canberkdurmus/microlab-2/image/1.jpg

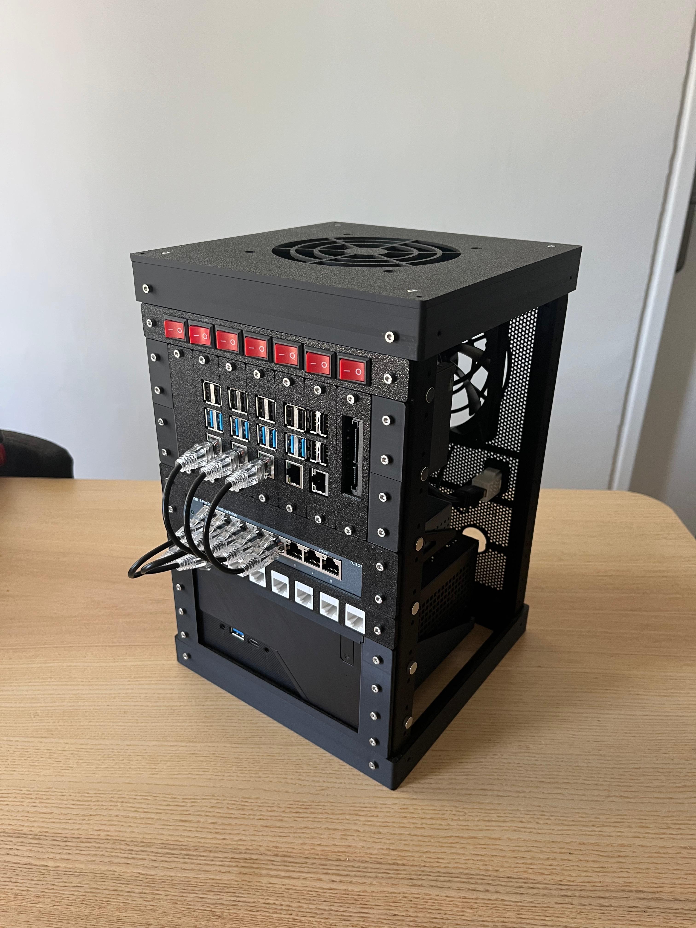
image/1.jpg
