canberkdurmus/microlab-2/image/2.jpg

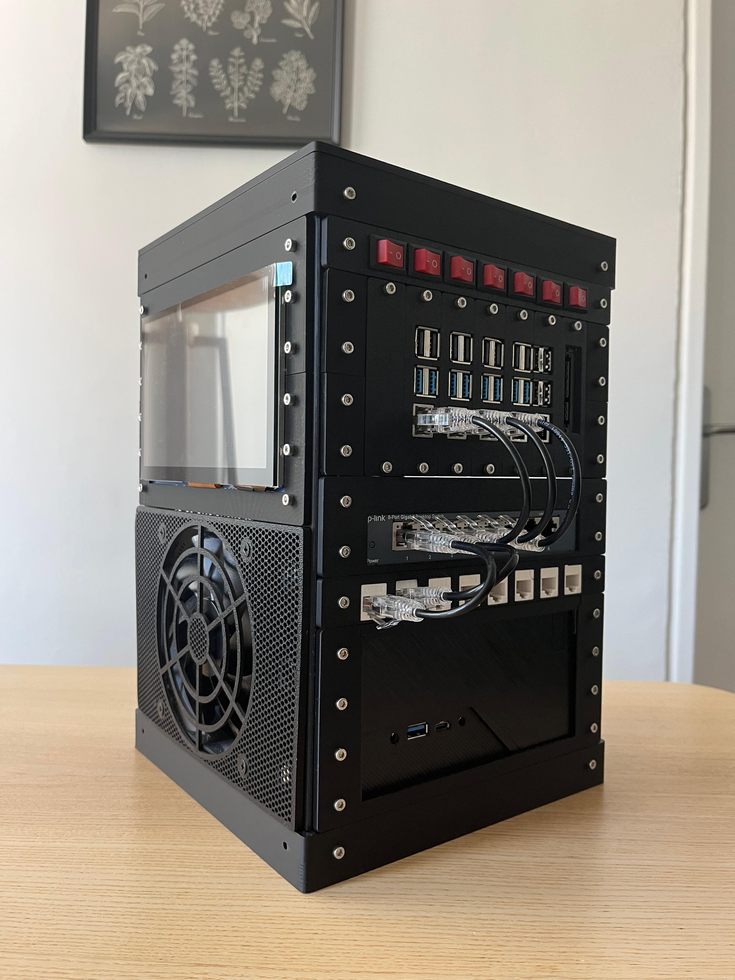
image/2.jpg
