canberkdurmus/microlab-2/image/4.jpg

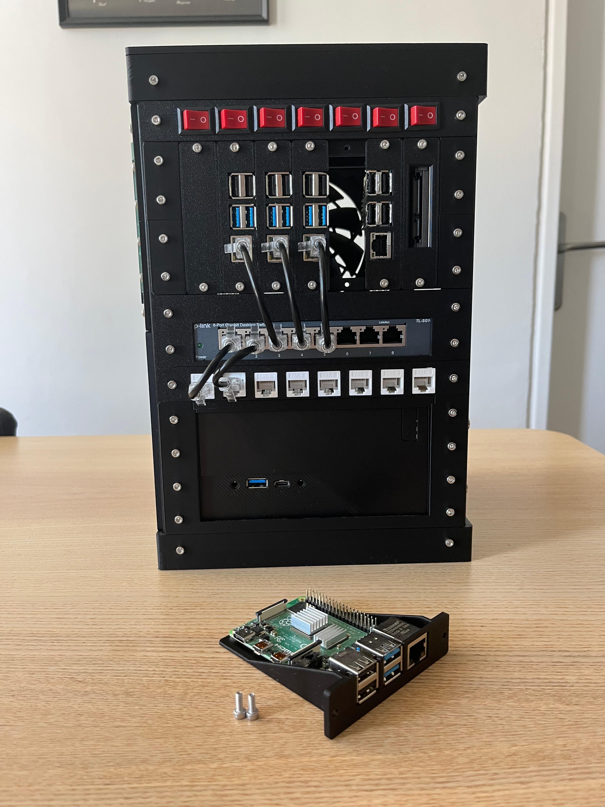
image/4.jpg
