canberkdurmus/microlab-2/image/5.jpg

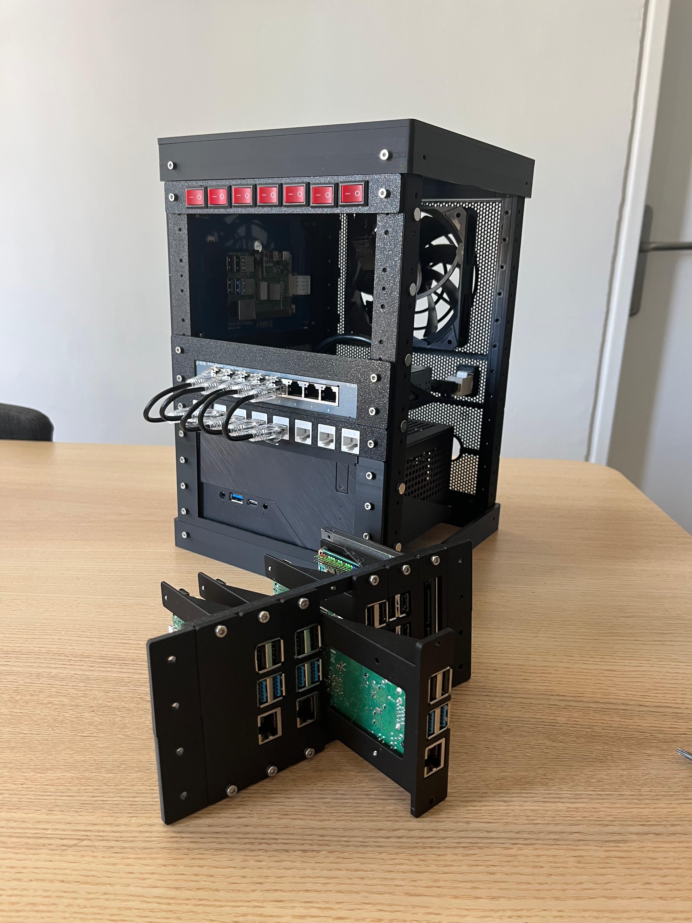
image/5.jpg
