canberkdurmus/microlab-2/image/6.jpg

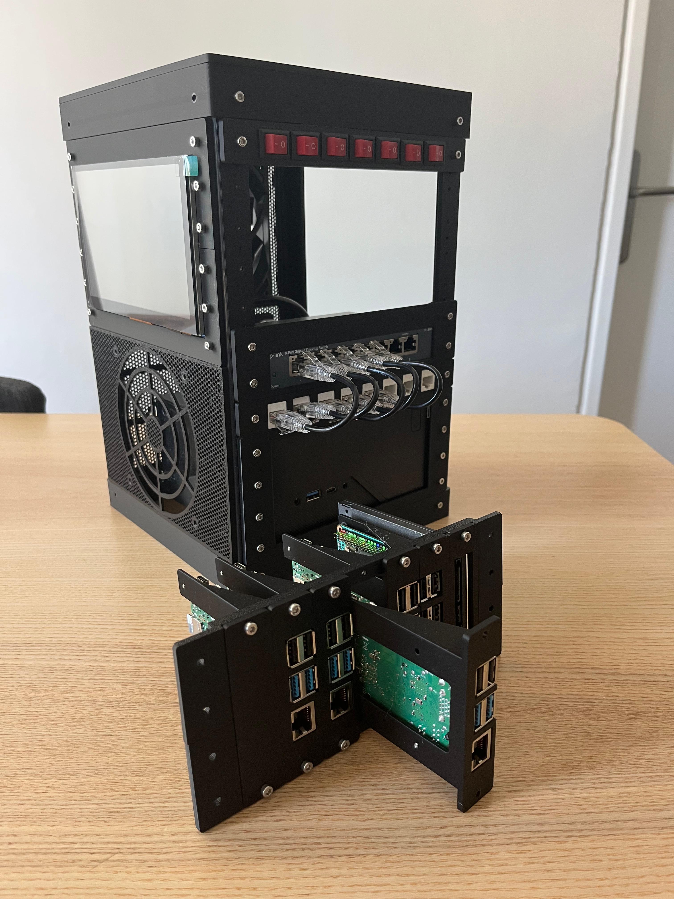
image/6.jpg
