canberkdurmus/microlab-2/image/7.jpg

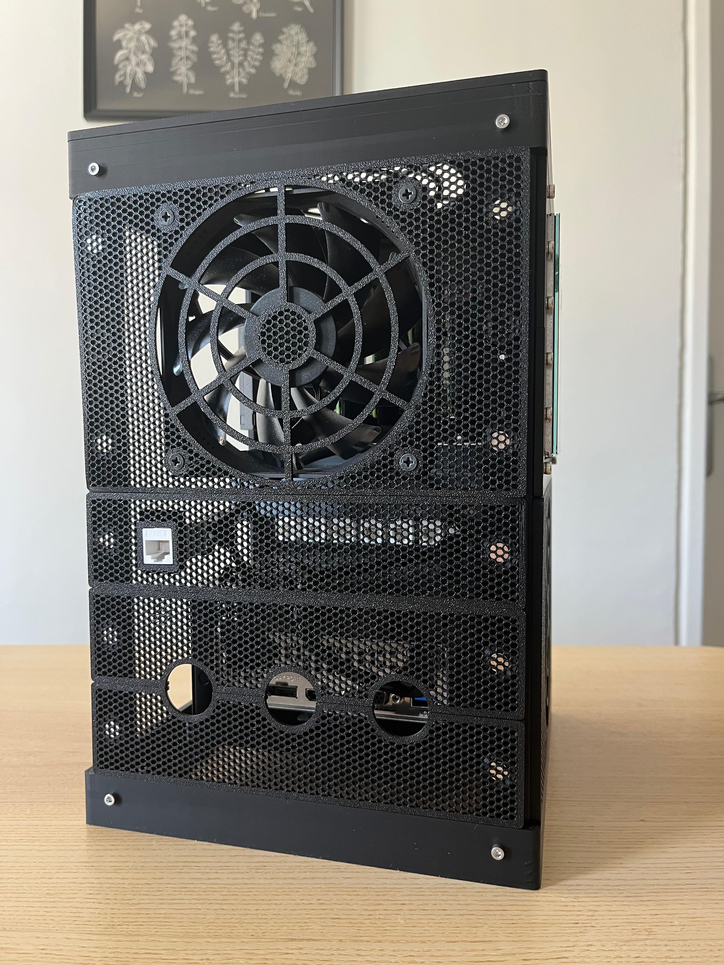
image/7.jpg
