canberkdurmus/microlab-2/image/8.jpg

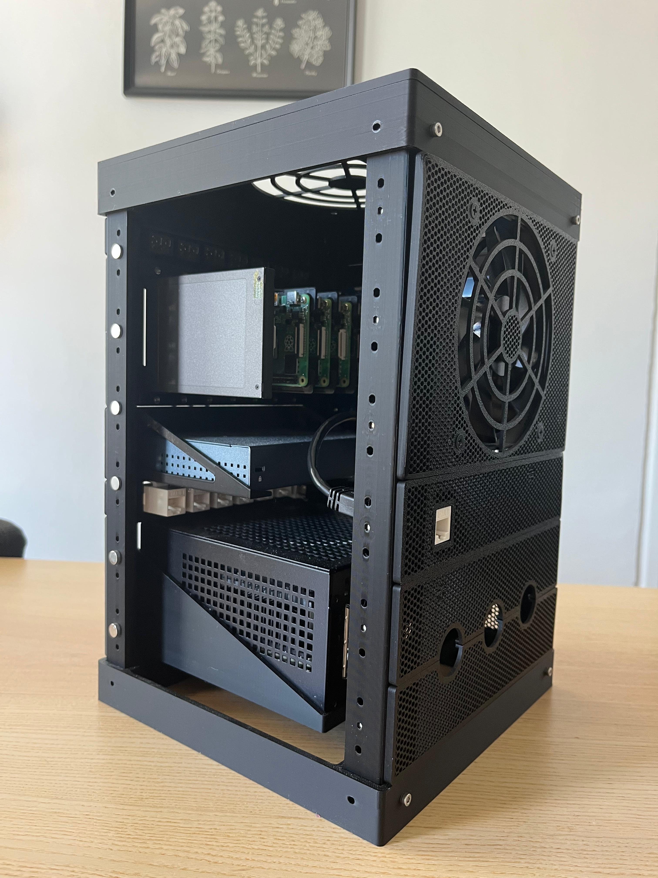
image/8.jpg
