canberkdurmus/microlab-2/image/9.jpg

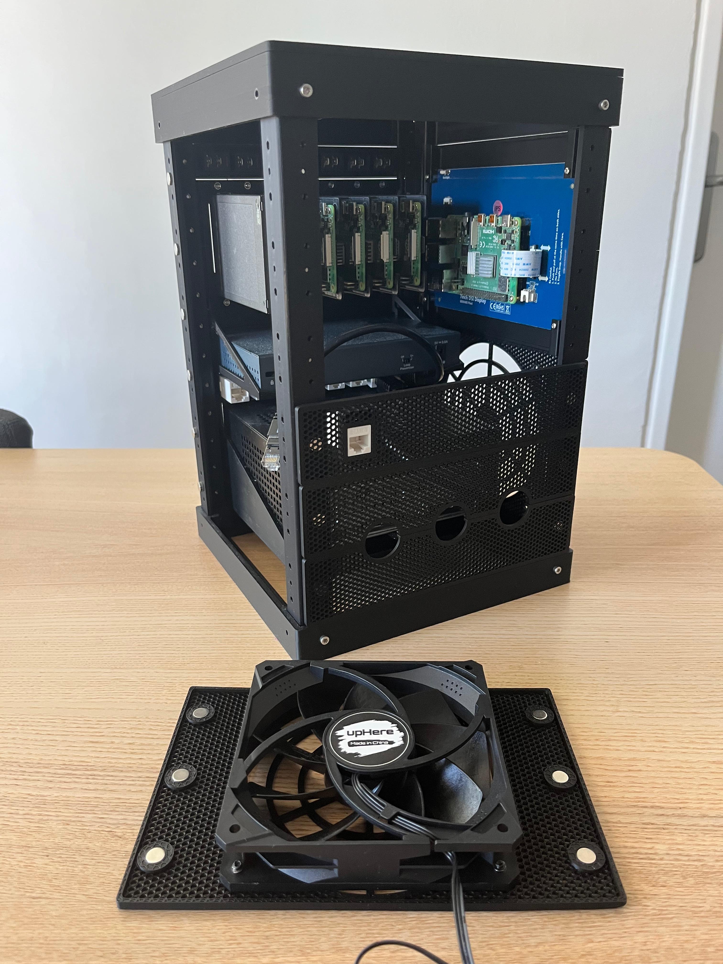
image/9.jpg
