canberkdurmus/microlab-2/image/10.jpg

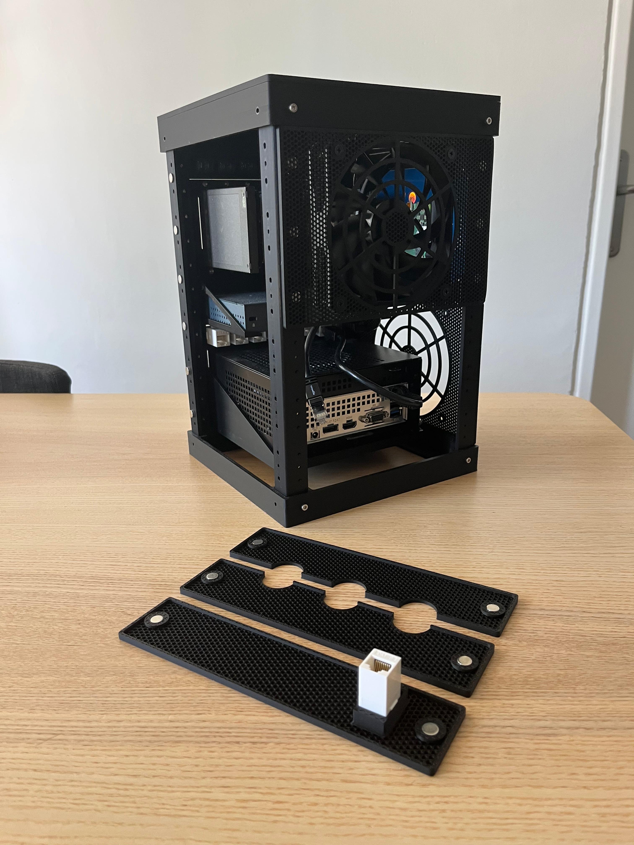
image/10.jpg
