canberkdurmus/microlab-2/image/11.jpg

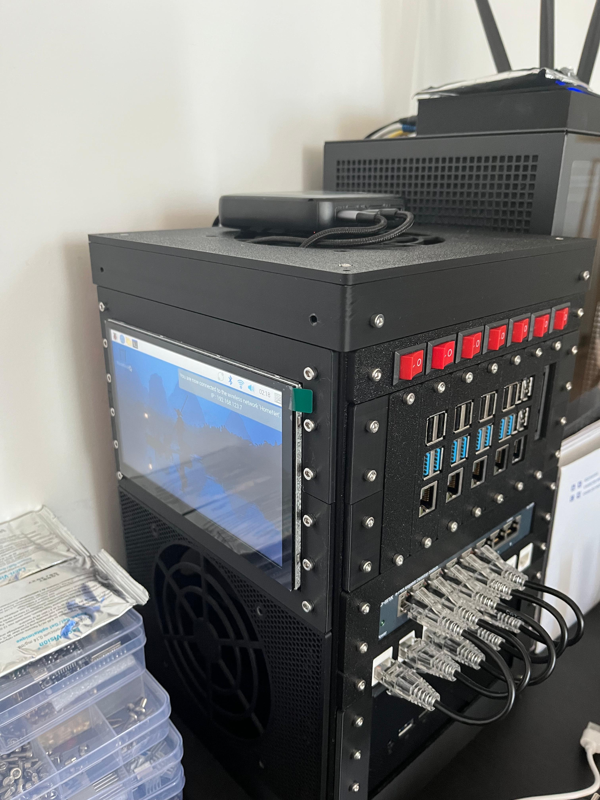
image/11.jpg
