canberkdurmus/microlab-2/step/Tray-0.5U-Template-Starter.step

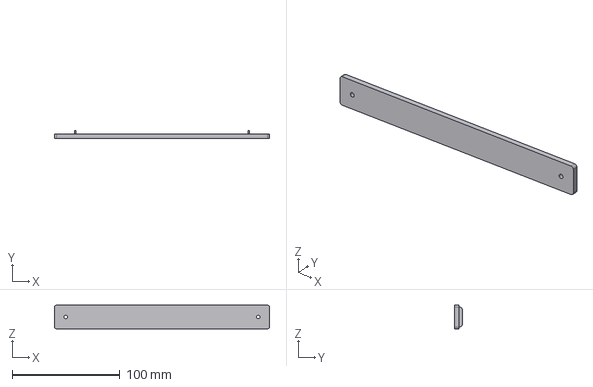
[picture p27: CAD file, 2025-09-13]
step/Tray-0.5U-Template-Starter.step
199.8 x 7.00 x 22.2 mm
