canberkdurmus/microlab-2/step/Extension-ITX-5U.step

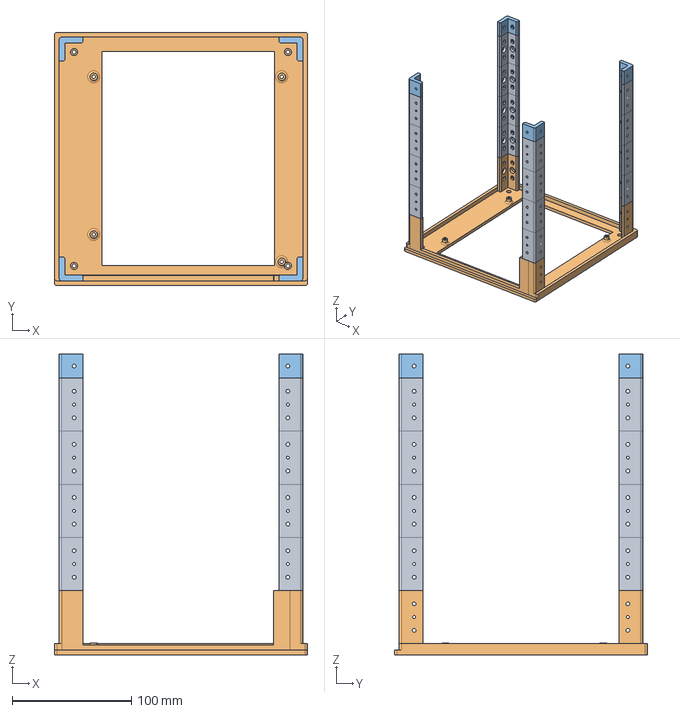
[picture p28: CAD file, 2025-09-13]
step/Extension-ITX-5U.step
212.0 x 212.0 x 252.1 mm
