canberkdurmus/microlab-2/step/Panel-1U-Button12mm.step

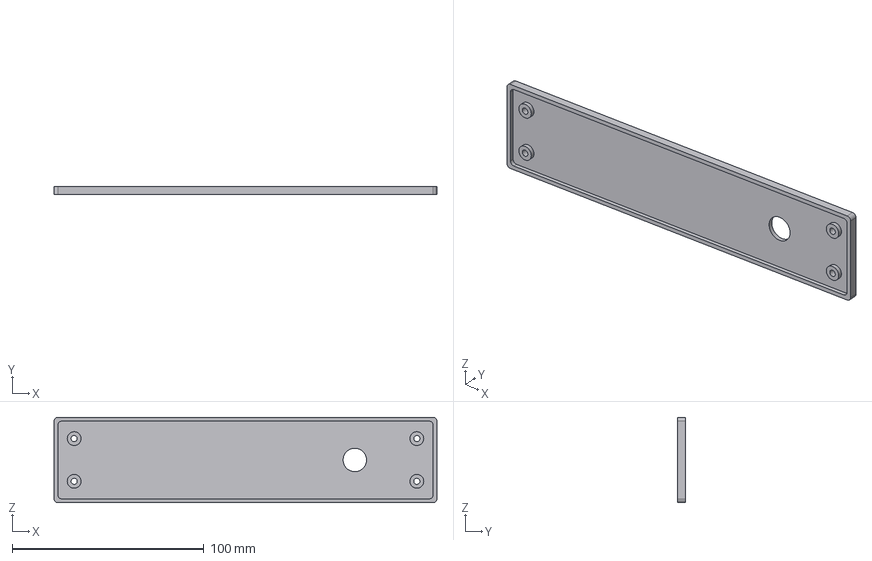
[picture p29: CAD file, 2025-09-13]
step/Panel-1U-Button12mm.step
199.6 x 4.00 x 44.4 mm
