canberkdurmus/microlab-2/step/Panel-3U-Disp7-Top.step

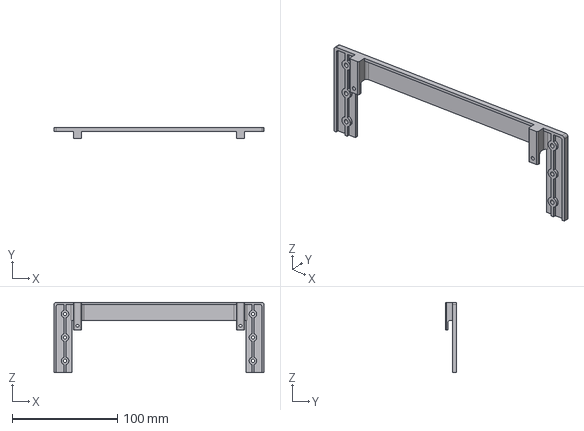
[picture p30: CAD file, 2025-09-13]
step/Panel-3U-Disp7-Top.step
199.6 x 10.5 x 66.7 mm
