canberkdurmus/microlab-2/step/Panel-1U-Mag-fan-40x3.step

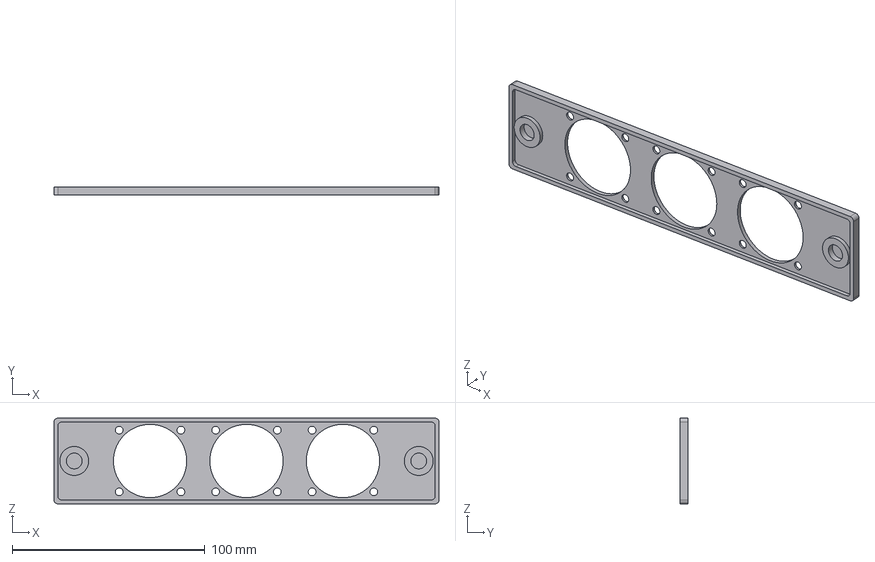
[picture p31: CAD file, 2025-09-13]
step/Panel-1U-Mag-fan-40x3.step
199.6 x 4.00 x 44.4 mm
