canberkdurmus/microlab-2/step/Tray-1U-Switch-TpLink-TLSG108.step

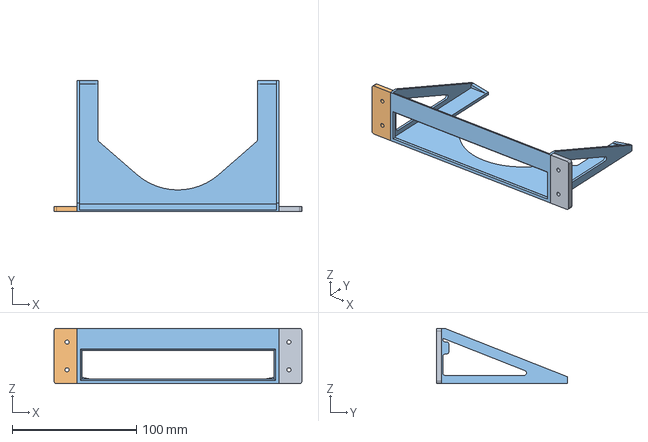
[picture p32: CAD file, 2025-09-13]
step/Tray-1U-Switch-TpLink-TLSG108.step
199.6 x 105.8 x 44.4 mm
