canberkdurmus/microlab-2/step/Tray-2U-X300.step

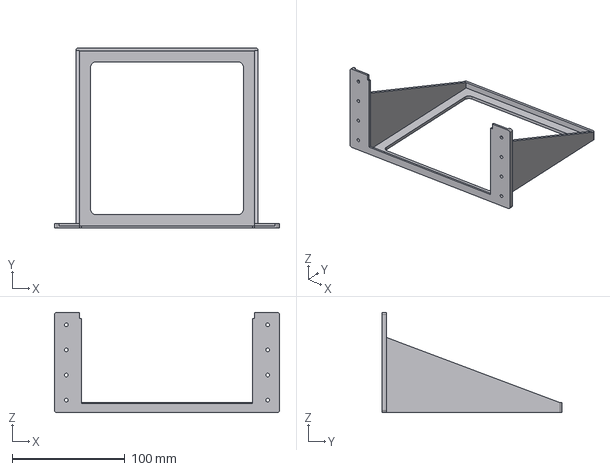
[picture p33: CAD file, 2025-09-13]
step/Tray-2U-X300.step
199.6 x 160.0 x 88.9 mm
