canberkdurmus/microlab-2/step/Mini-Tray-0.5-Blank.step

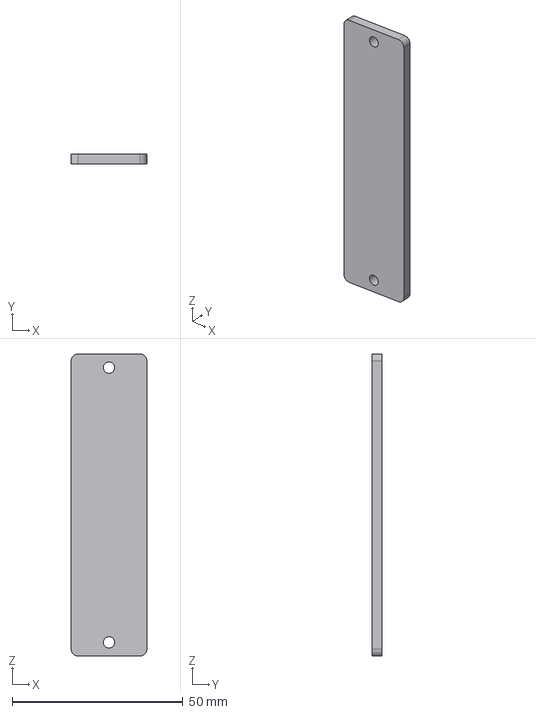
[picture p34: CAD file, 2025-09-13]
step/Mini-Tray-0.5-Blank.step
22.2 x 3.00 x 88.5 mm
