canberkdurmus/microlab-2/step/Extension-ITX-1U.step

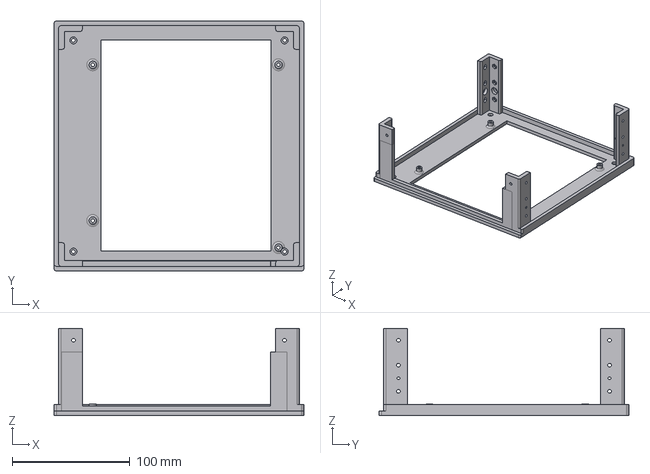
[picture p35: CAD file, 2025-09-13]
step/Extension-ITX-1U.step
212.0 x 212.0 x 74.1 mm
