canberkdurmus/microlab-2/step/Panel-3U-Solid.step

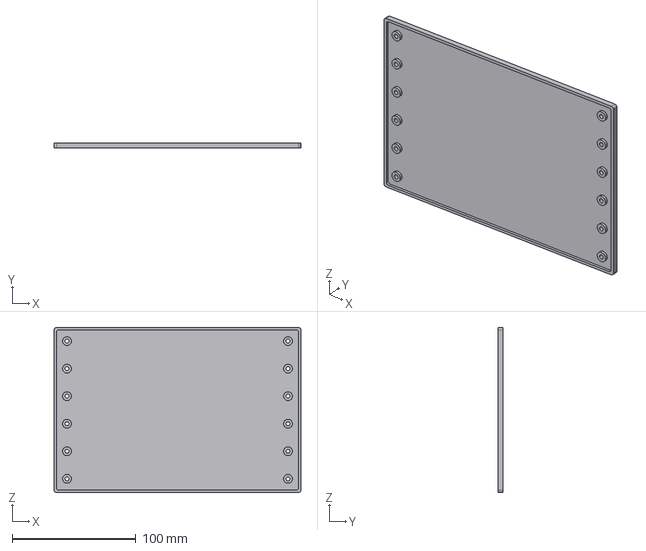
[picture p36: CAD file, 2025-09-13]
step/Panel-3U-Solid.step
199.6 x 4.00 x 133.5 mm
