canberkdurmus/microlab-2/step/Tray-1U-Template-Starter-2.step

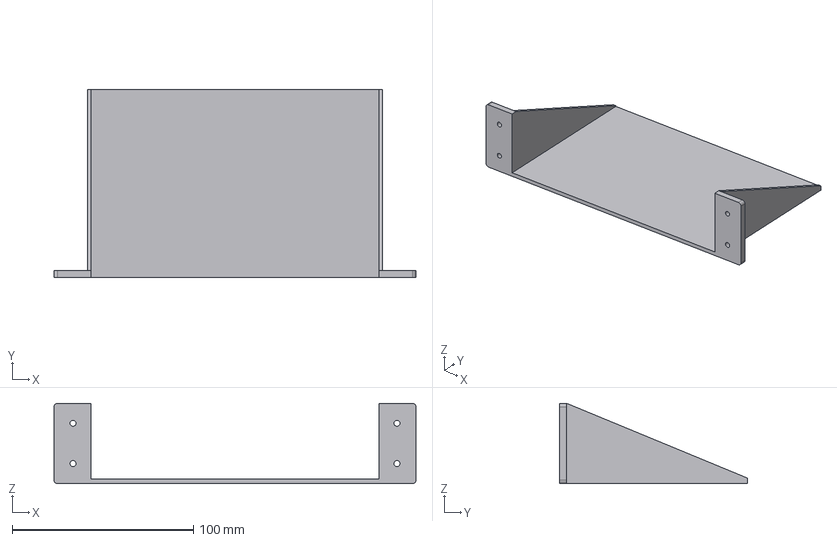
[picture p38: CAD file, 2025-09-13]
step/Tray-1U-Template-Starter-2.step
199.8 x 104.0 x 44.4 mm
