canberkdurmus/microlab-2/step/Panel-1U-8xKeystone.step

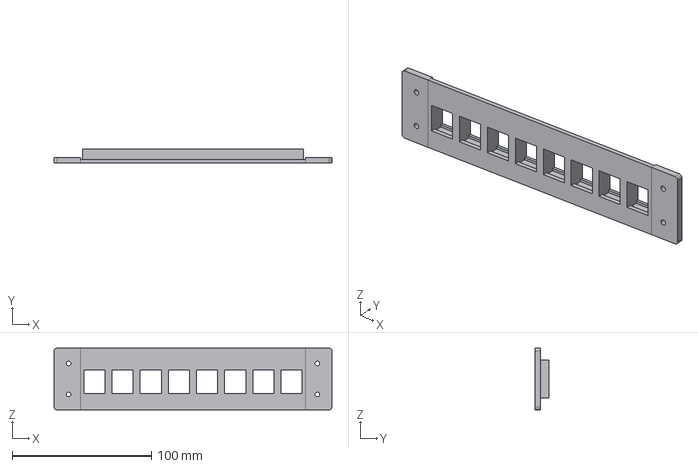
[picture p39: CAD file, 2025-09-13]
step/Panel-1U-8xKeystone.step
199.8 x 10.2 x 44.4 mm
