canberkdurmus/microlab-2/step/Panel-4U-Solid.step

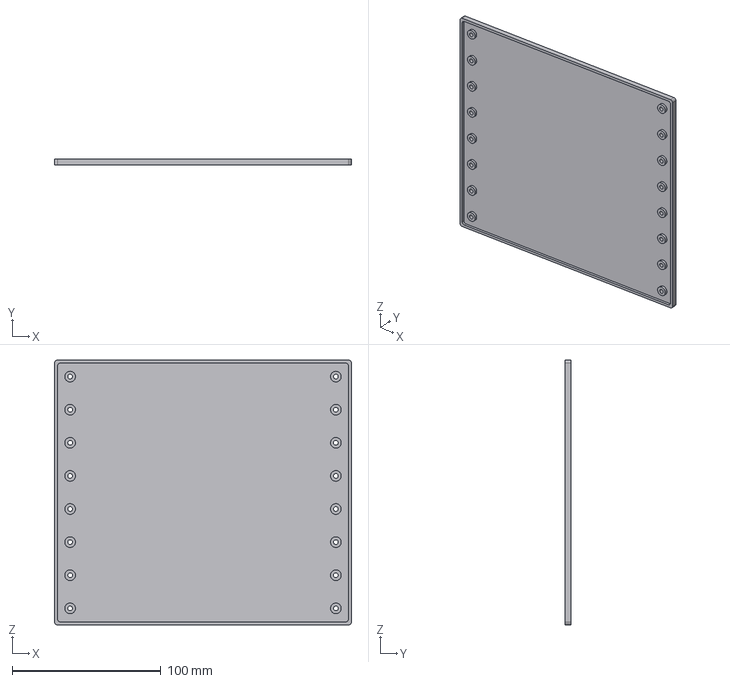
[picture p40: CAD file, 2025-09-13]
step/Panel-4U-Solid.step
199.6 x 4.00 x 177.9 mm
