canberkdurmus/microlab-2/step/Top-Panel-Solid.step

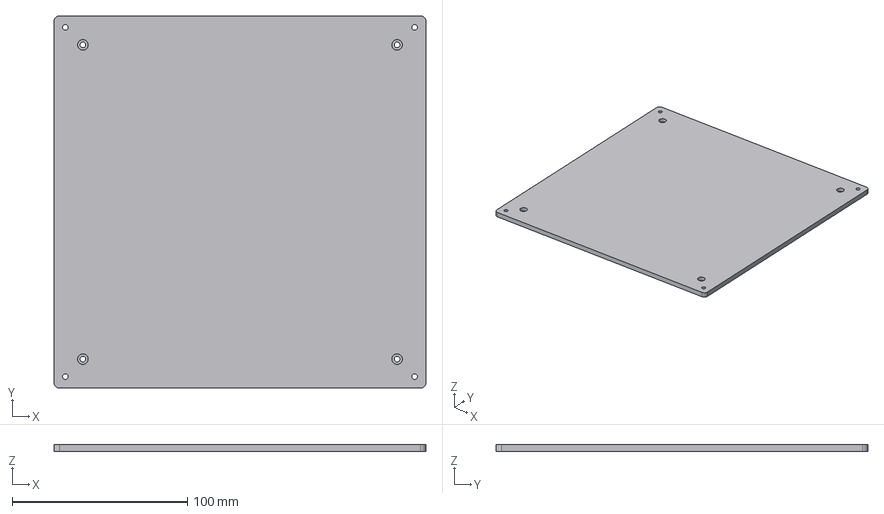
[picture p41: CAD file, 2025-09-13]
step/Top-Panel-Solid.step
212.0 x 212.0 x 4.00 mm
