canberkdurmus/microlab-2/step/Panel-0.5U-Keystone8.step

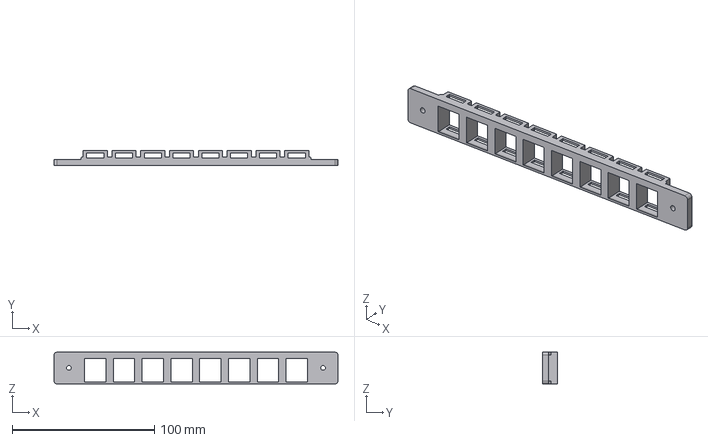
[picture p42: CAD file, 2025-09-13]
step/Panel-0.5U-Keystone8.step
199.8 x 10.2 x 22.2 mm
