canberkdurmus/microlab-2/step/Panel-2U-fan-60.step

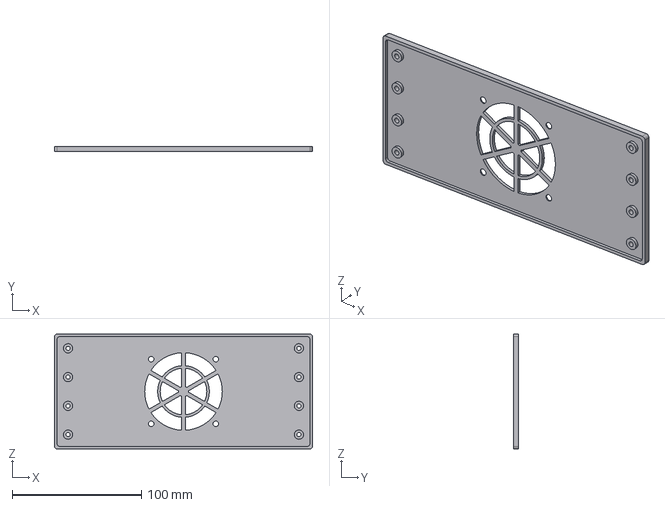
[picture p43: CAD file, 2025-09-13]
step/Panel-2U-fan-60.step
199.6 x 4.00 x 88.9 mm
