canberkdurmus/microlab-2/step/Structure-Col-Guard-6U.step

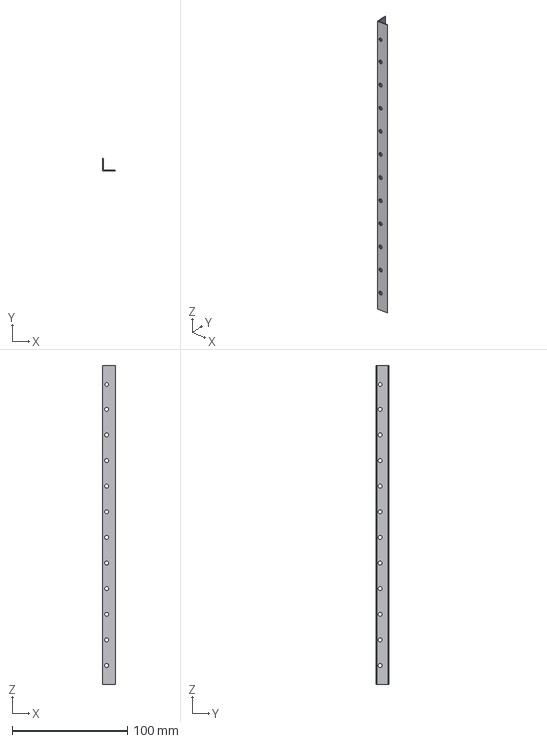
[picture p44: CAD file, 2025-09-13]
step/Structure-Col-Guard-6U.step
11.0 x 11.0 x 277.0 mm
