canberkdurmus/microlab-2/step/Tray-1U-GMKTec-G3.step

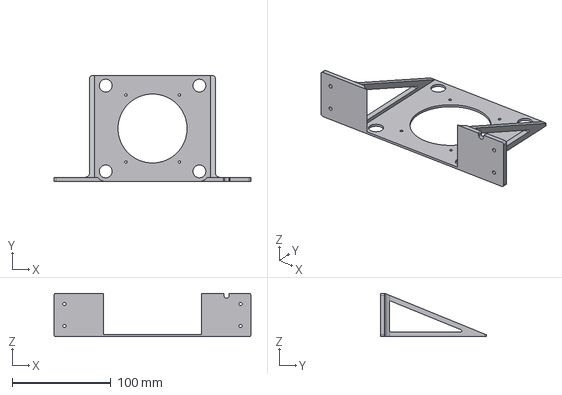
[picture p46: CAD file, 2025-09-13]
step/Tray-1U-GMKTec-G3.step
199.8 x 107.0 x 44.0 mm
