canberkdurmus/microlab-2/step/Tray-2U-X300-Acc.step

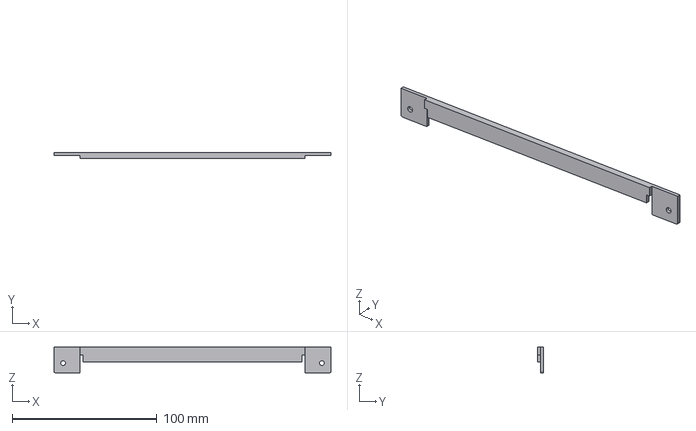
[picture p47: CAD file, 2025-09-13]
step/Tray-2U-X300-Acc.step
191.2 x 4.00 x 17.8 mm
