canberkdurmus/microlab-2/step/Structure-Cap-v2.step

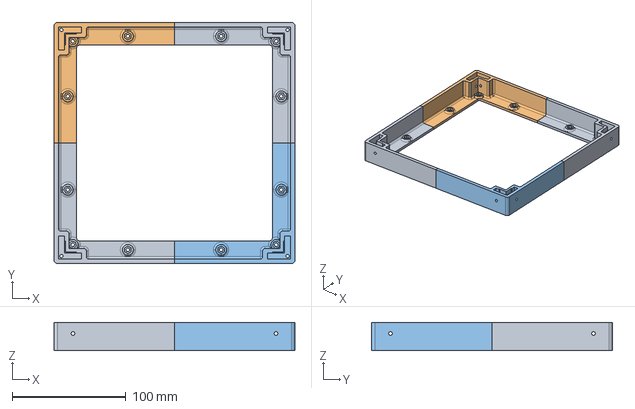
[picture p48: CAD file, 2025-09-13]
step/Structure-Cap-v2.step
212.0 x 212.0 x 24.8 mm
