canberkdurmus/microlab-2/step/Tray-1.5U-SFX-L.step

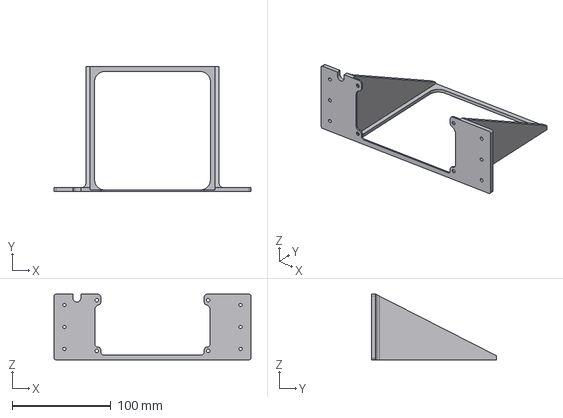
[picture p49: CAD file, 2025-09-13]
step/Tray-1.5U-SFX-L.step
199.8 x 126.5 x 66.7 mm
