canberkdurmus/microlab-2/step/Top-Panel-Fan-120.step

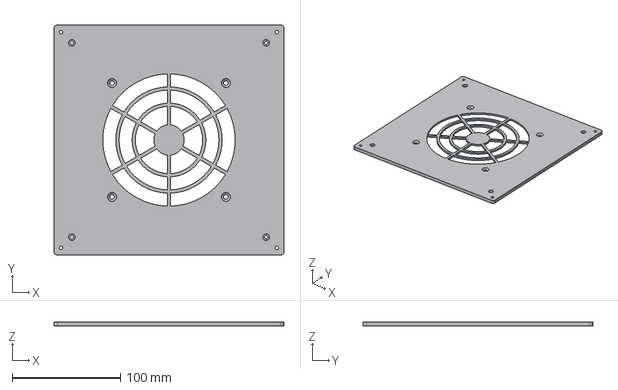
[picture p50: CAD file, 2025-09-13]
step/Top-Panel-Fan-120.step
212.0 x 212.0 x 4.00 mm
