canberkdurmus/microlab-2/step/Mini-Tray-0.5-RPi5.step

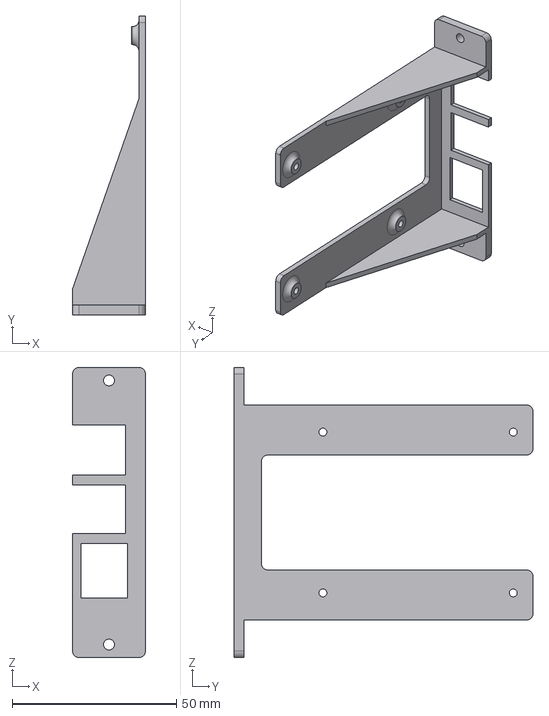
[picture p51: CAD file, 2025-09-13]
step/Mini-Tray-0.5-RPi5.step
22.2 x 91.1 x 88.5 mm
