canberkdurmus/microlab-2/step/Extension-ITX-4U.step

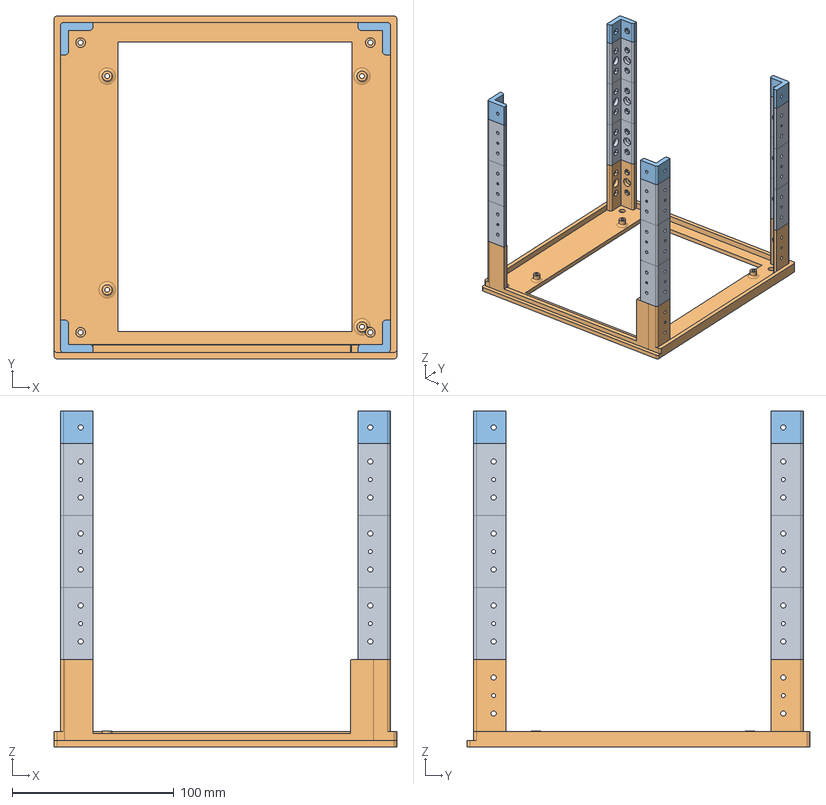
[picture p52: CAD file, 2025-09-13]
step/Extension-ITX-4U.step
212.0 x 212.0 x 207.6 mm
