canberkdurmus/microlab-2/step/Mini-Tray-0.5-SATA2.5.step

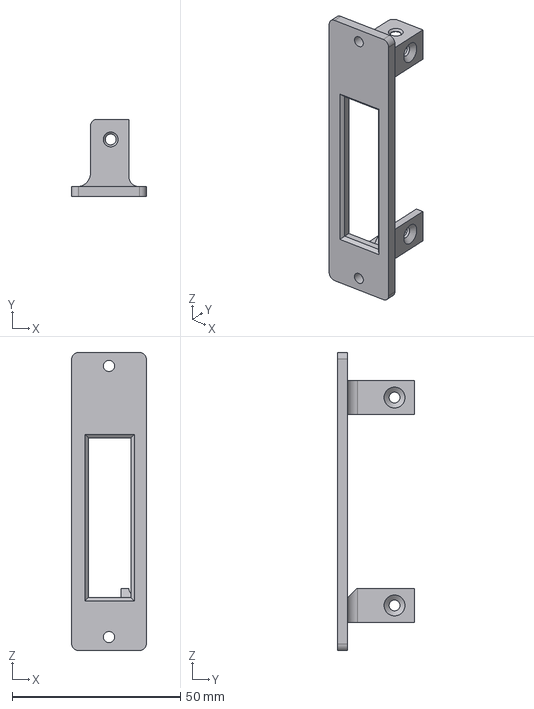
[picture p53: CAD file, 2025-09-13]
step/Mini-Tray-0.5-SATA2.5.step
22.2 x 23.0 x 88.5 mm
