canberkdurmus/microlab-2/step/Extension-ITX-3U.step

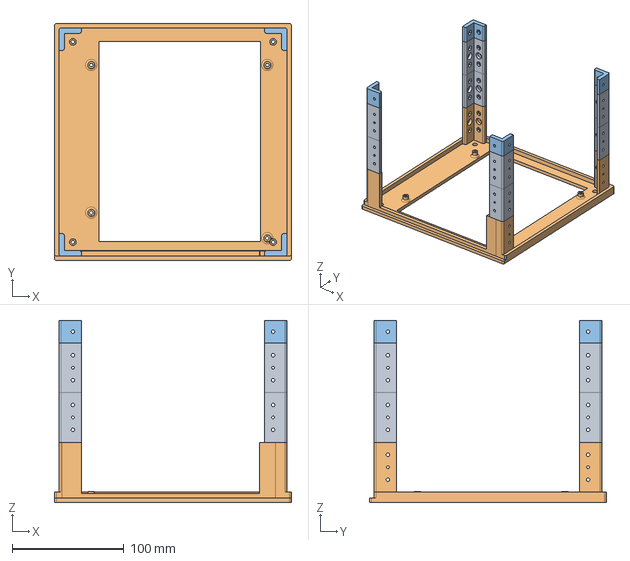
[picture p55: CAD file, 2025-09-13]
step/Extension-ITX-3U.step
212.0 x 212.0 x 163.1 mm
