canberkdurmus/microlab-2/step/Structure-Mid-Extender.step

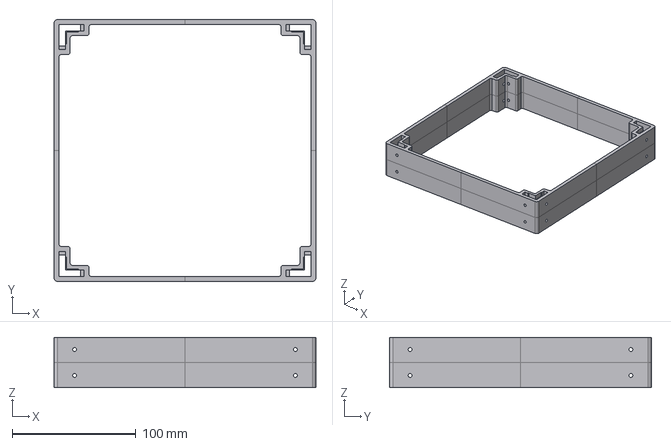
[picture p56: CAD file, 2025-09-13]
step/Structure-Mid-Extender.step
212.0 x 212.0 x 40.5 mm
