canberkdurmus/microlab-2/step/Structure-Col-6U-dual-magnet.step

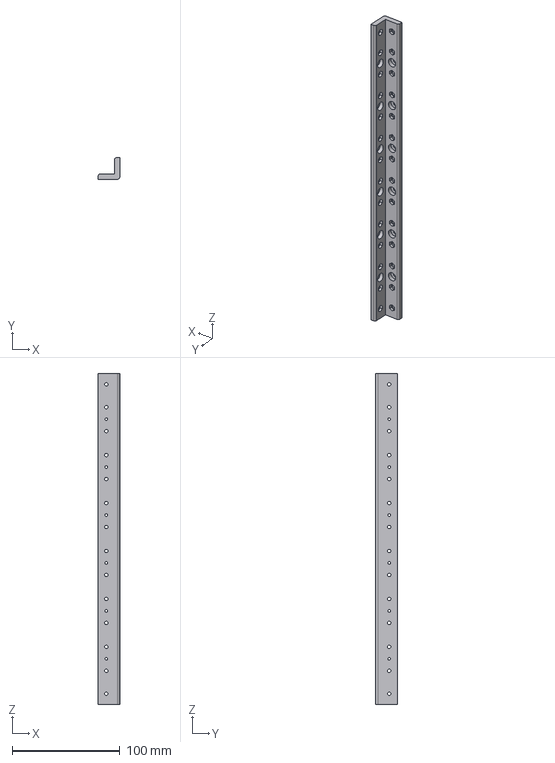
[picture p57: CAD file, 2025-09-13]
step/Structure-Col-6U-dual-magnet.step
20.0 x 20.0 x 307.2 mm
