canberkdurmus/microlab-2/step/Tray-0.5U-RPi4x2.step

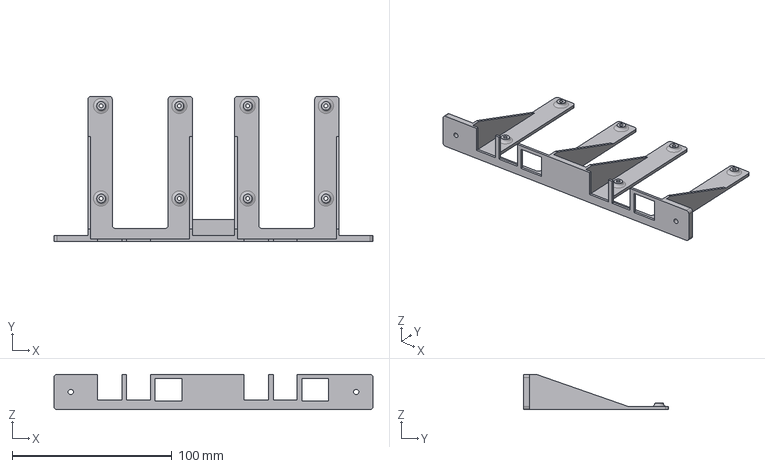
[picture p58: CAD file, 2025-09-13]
step/Tray-0.5U-RPi4x2.step
199.8 x 91.1 x 22.2 mm
