canberkdurmus/microlab-2/step/Tray-0.5U-Switch-Tenda-SG108.step

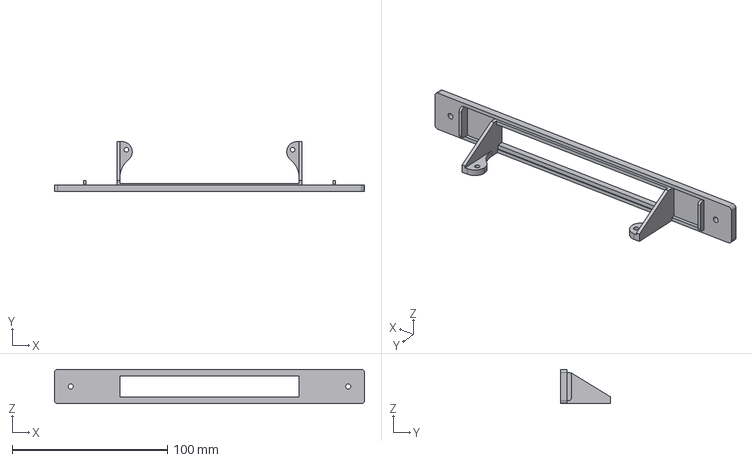
[picture p59: CAD file, 2025-09-13]
step/Tray-0.5U-Switch-Tenda-SG108.step
199.8 x 32.0 x 22.2 mm
