canberkdurmus/microlab-2/step/Mini-Frame-3.5U-2.step

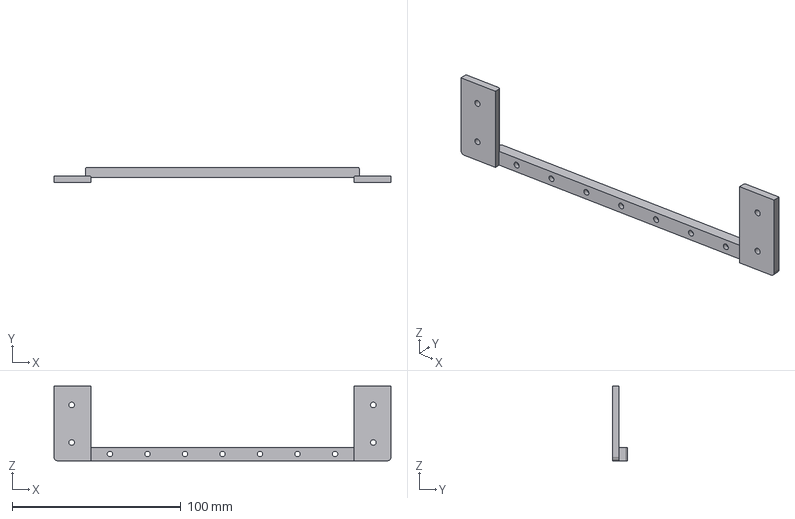
[picture p60: CAD file, 2025-09-13]
step/Mini-Frame-3.5U-2.step
199.8 x 9.00 x 44.2 mm
