canberkdurmus/microlab-2/step/Panel-0.5U-Solid.step

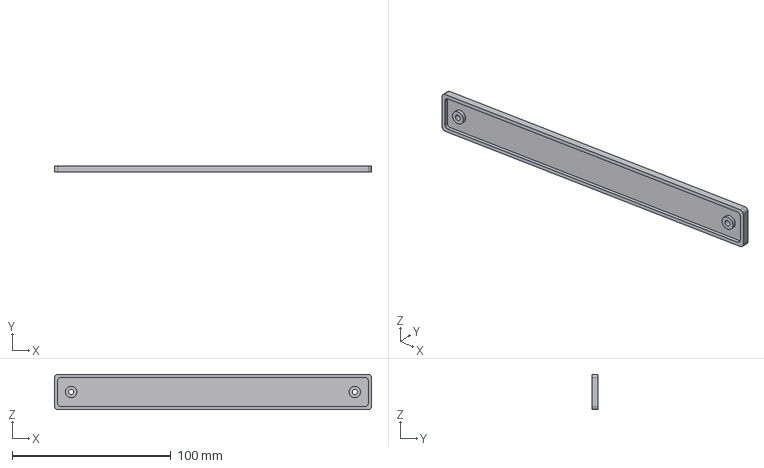
[picture p61: CAD file, 2025-09-13]
step/Panel-0.5U-Solid.step
199.6 x 4.00 x 22.2 mm
