canberkdurmus/microlab-2/step/Tray-0.5U-RPi4-SATA.step

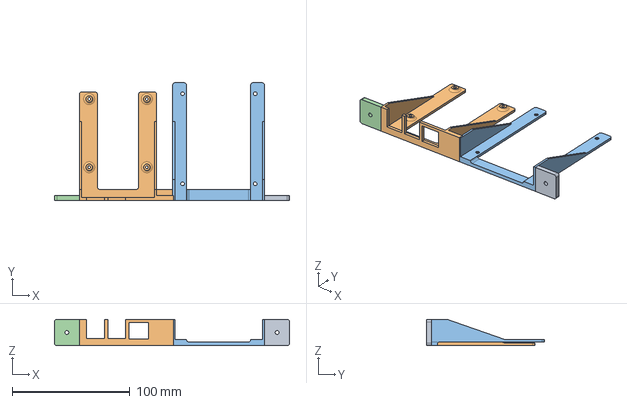
[picture p62: CAD file, 2025-09-13]
step/Tray-0.5U-RPi4-SATA.step
199.8 x 100.0 x 22.2 mm
