canberkdurmus/microlab-2/step/Extension-ITX-2U.step

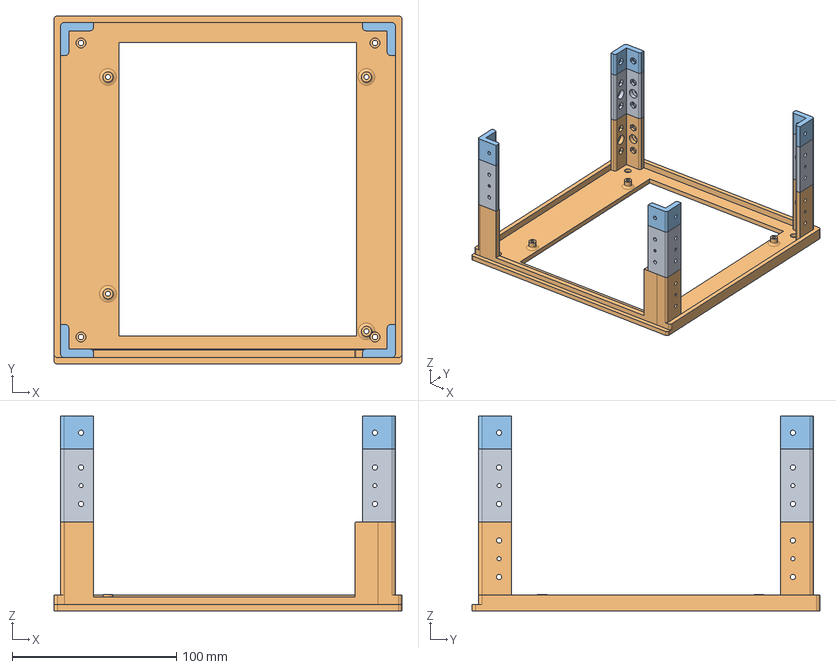
[picture p63: CAD file, 2025-09-13]
step/Extension-ITX-2U.step
212.0 x 212.0 x 118.6 mm
